SasaKuruppuarachchi/jetson-cv-hub/calibration/raw/calib_t265/results_20210930T172527_gyro.png

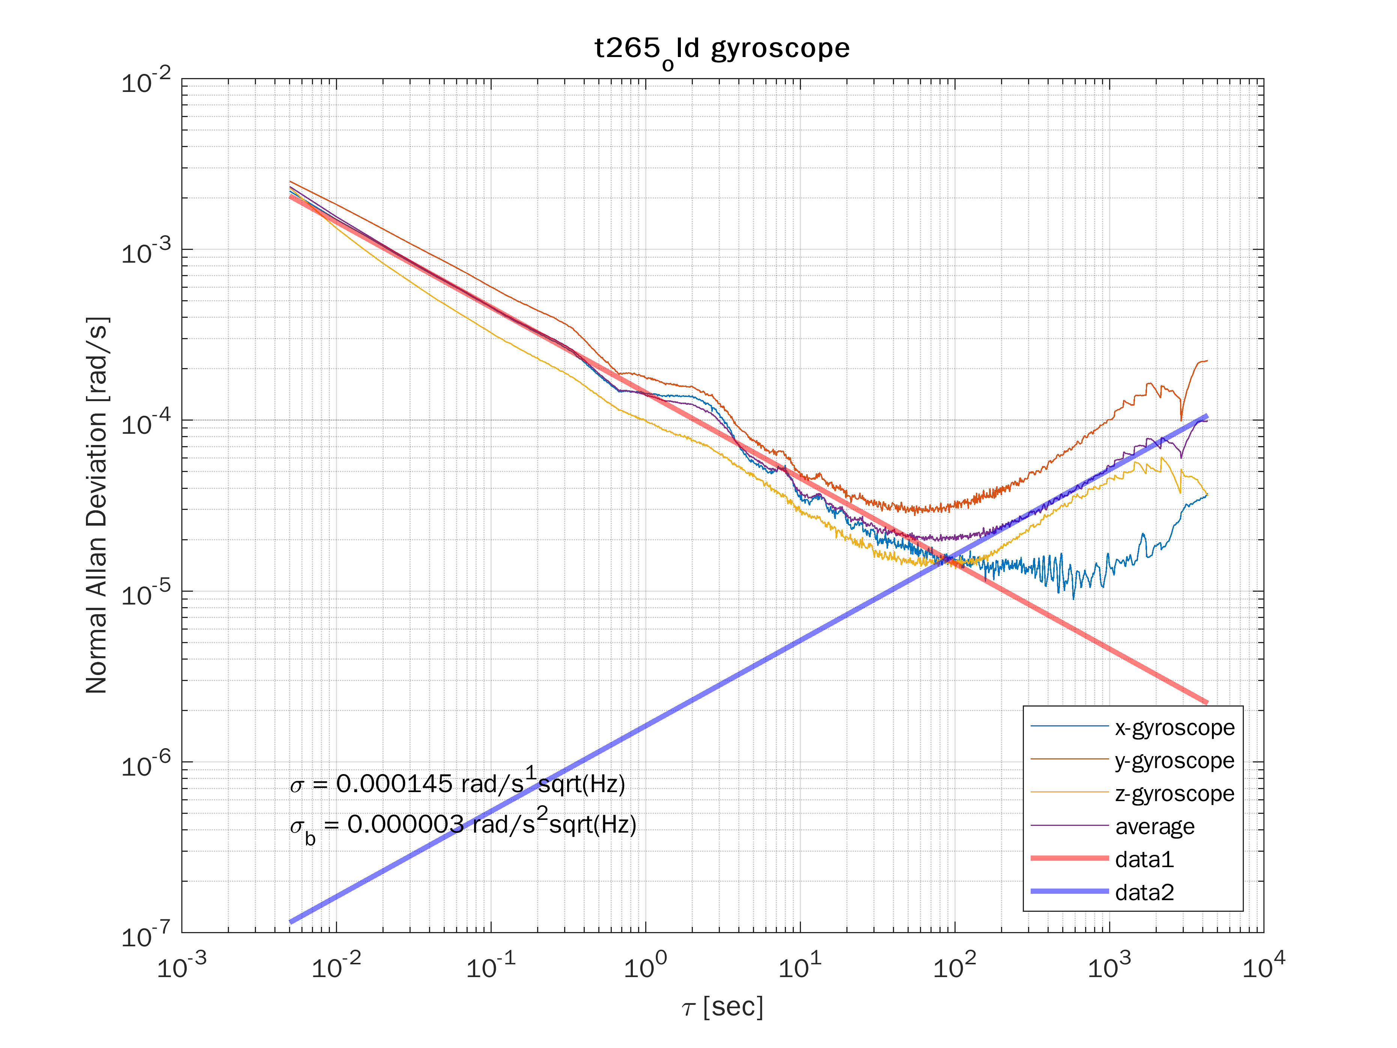
calibration/raw/calib_t265/results_20210930T172527_gyro.png
