SasaKuruppuarachchi/jetson-cv-hub/calibration/raw/Flir calib/IMU/accel.png

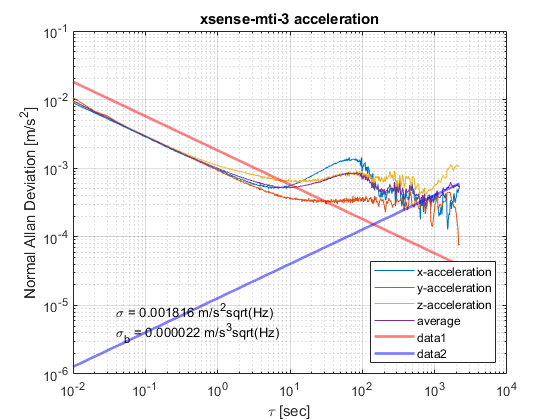
calibration/raw/Flir calib/IMU/accel.png
