SasaKuruppuarachchi/jetson-cv-hub/calibration/raw/very good calib 2/vingette_0.png

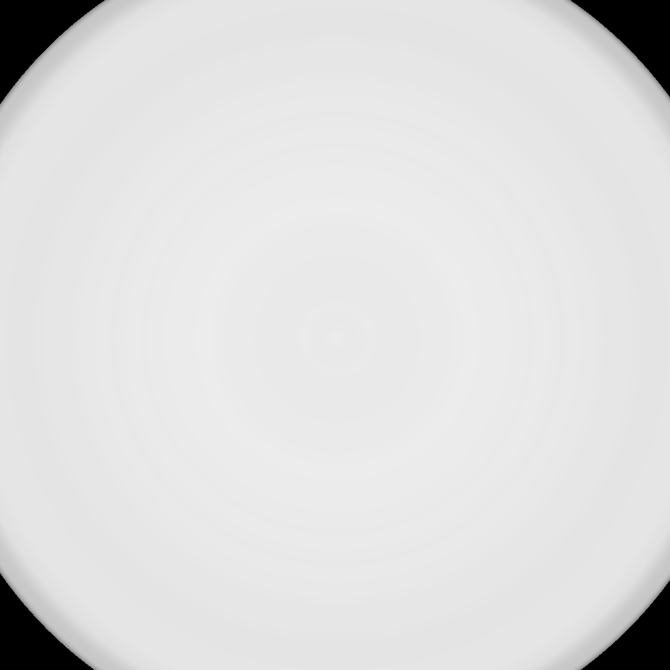
calibration/raw/very good calib 2/vingette_0.png
