SasaKuruppuarachchi/jetson-cv-hub/calibration/raw/very good calib 2/vingette_1.png

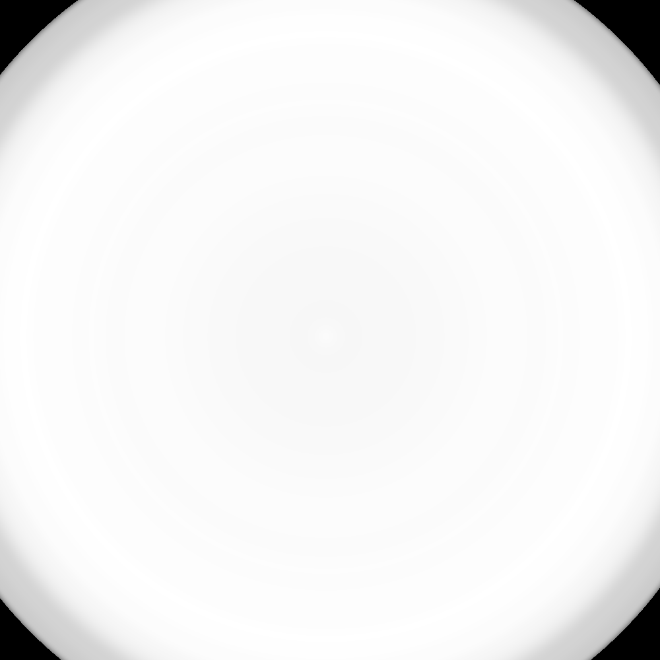
calibration/raw/very good calib 2/vingette_1.png
