SasaKuruppuarachchi/jetson-cv-hub/calibration/raw/calib_t265/Eval/plots/traj_est/trajectory_side_sim3_-1.pdf

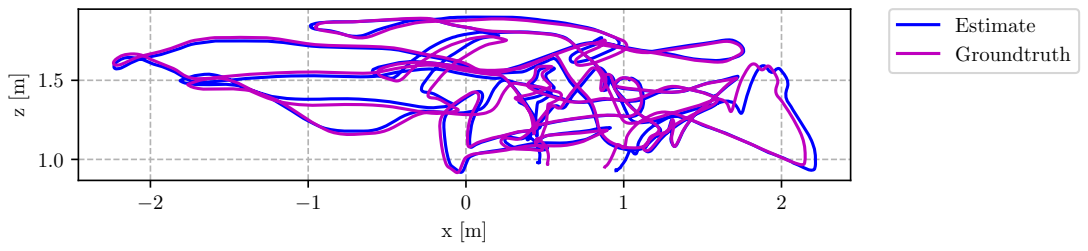
[picture p32: page 1]
Estimate Groundtruth
