SasaKuruppuarachchi/jetson-cv-hub/calibration/raw/calib_t265/Eval/plots/traj_est/trajectory_top_posyaw_-1.pdf

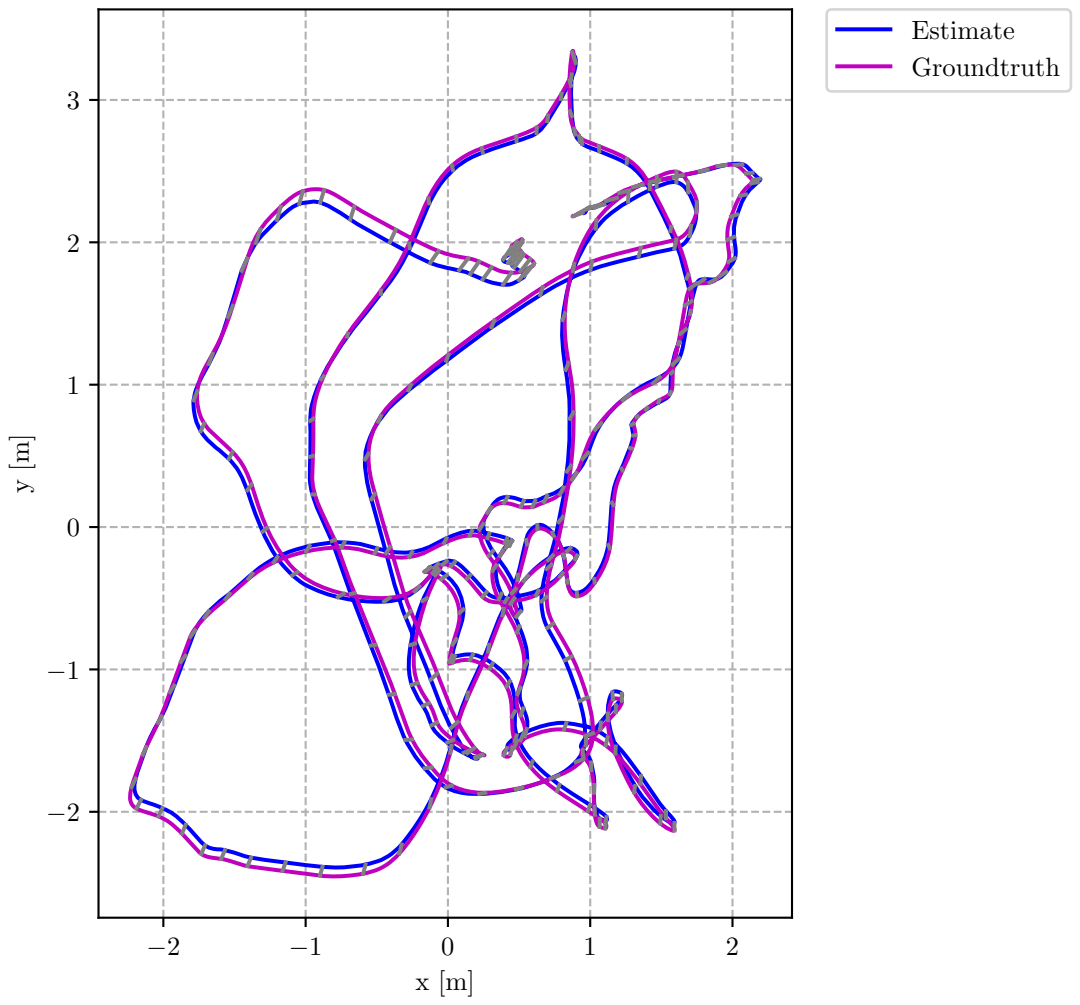
[picture p33: page 1]
Estimate Groundtruth
