SasaKuruppuarachchi/jetson-cv-hub/calibration/raw/calib_t265/Eval/plots/traj_est/trajectory_top_sim3_-1.pdf

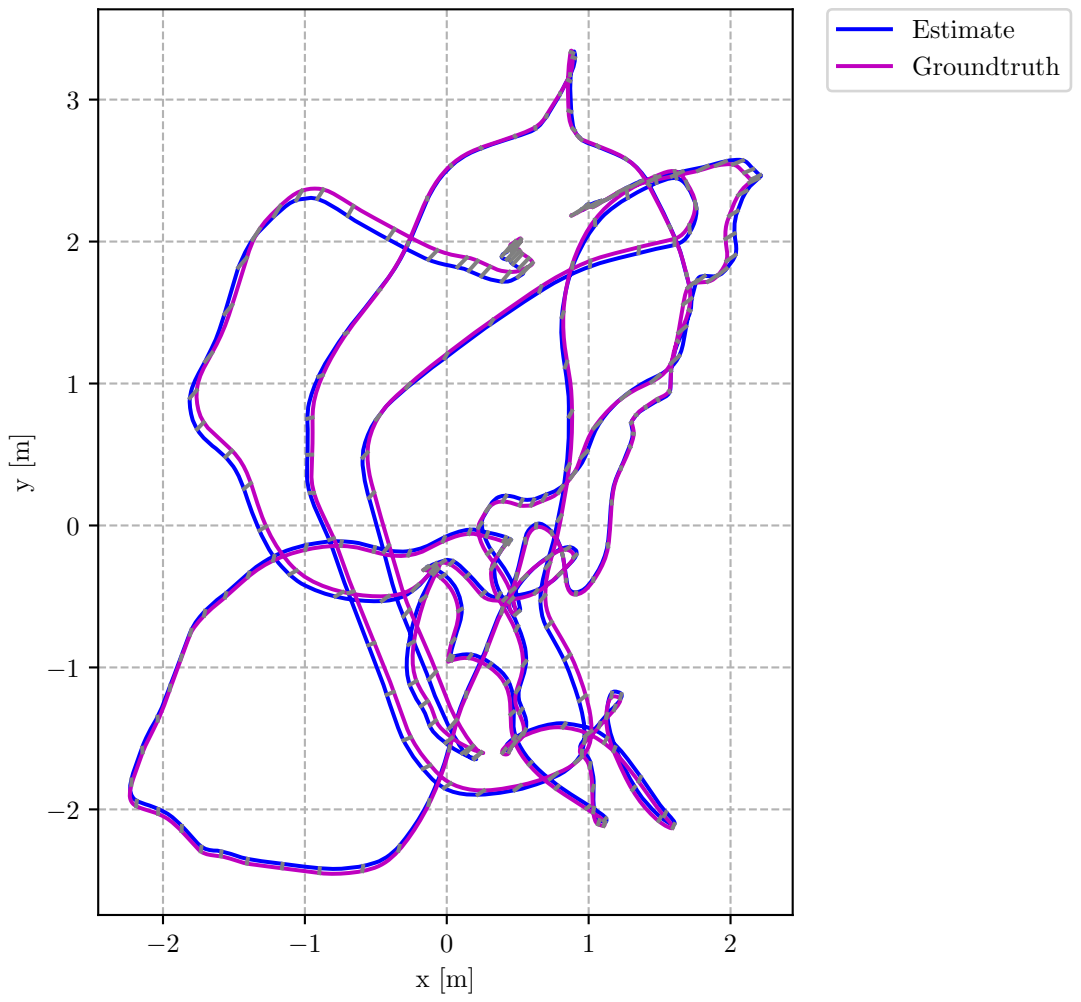
[picture p34: page 1]
Estimate Groundtruth
