SasaKuruppuarachchi/jetson-cv-hub/calibration/raw/calib_t265/Eval/plots/traj_est/translation_error_posyaw_-1.pdf

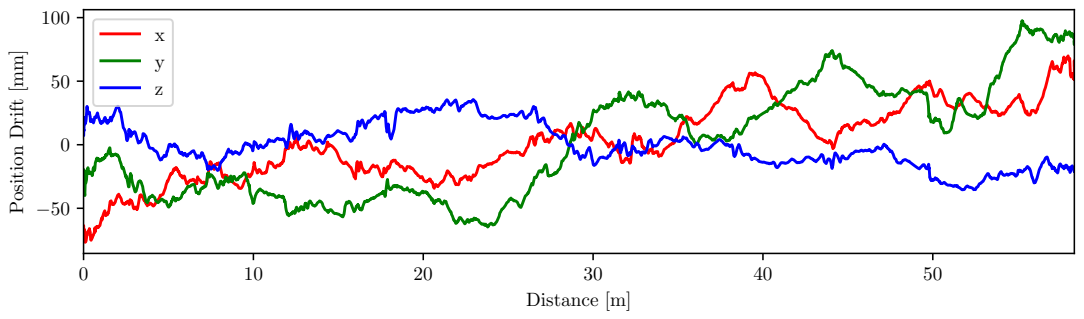
[picture p55: page 1]
Distance [m]; Position Drift [mm]; xyz
