SasaKuruppuarachchi/jetson-cv-hub/calibration/raw/calib_t265/Eval/plots/traj_est/translation_error_sim3_-1.pdf

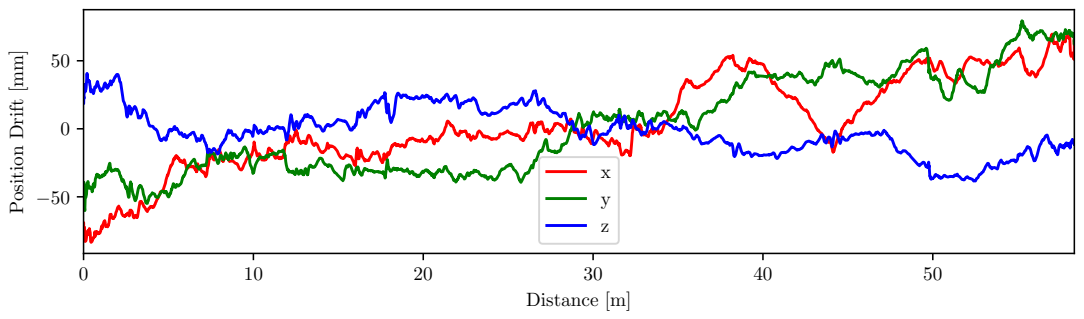
[picture p56: page 1]
Distance [m]; xyz

Position Drift [mm]
